maticas-org/maticas-data-logger/src/arduino/datalogger-esp32-dev-board/Event.cpp

#include "Event.h"

Event::Event() {
    type_ = UNKNOWN_EVENT; // Initialize with an unknown type
    statusCode_ = -1;
    timestamp_ = "";
    data_ = "{}";
}

Event::Event(int type,
             int statusCode,
             const String& timestamp,
             const String& data) {
    type_ = type;
    statusCode_ = statusCode;
    timestamp_ = timestamp;
    data_ = data;
}

Event::Event(String eventString){

    //parse the string to get the event attributes
    int typeIndex = eventString.indexOf("\"type\":") + 7;
    int statusCodeIndex = eventString.indexOf("\"statusCode\":") + 14;
    int timestampIndex = eventString.indexOf("\"datetime\":\"") + 12;
    int dataIndex = eventString.indexOf("\"data\":") + 7;

    type_ = eventString.substring(typeIndex, eventString.indexOf(",", typeIndex)).toInt();
    statusCode_ = eventString.substring(statusCodeIndex, eventString.indexOf(",", statusCodeIndex)).toInt();
    timestamp_ = eventString.substring(timestampIndex, eventString.indexOf("\",", timestampIndex));
    data_ = eventString.substring(dataIndex, eventString.indexOf("timesSent") - 2);
    timesSent = eventString.substring(eventString.indexOf("timesSent") + 11, eventString.indexOf("}", eventString.indexOf("timesSent"))).toInt();
}

int Event::getType() const {
    return type_;
}

int Event::getStatusCode() const {
    return statusCode_;
}

String Event::getTimestamp() const {
    return timestamp_;
}

String Event::getData() const {
    return data_;
}

void Event::setTimestamp(const String& timestamp) {
    timestamp_ = timestamp;
}


String Event::toString() const {

    //json like string representation
    String eventString = "{";
    eventString += "\"type\":";
    eventString += type_;
    eventString += ",\"statusCode\":";
    eventString += statusCode_;
    eventString += ",\"datetime\":\"";
    eventString += timestamp_;
    eventString += "\",\"data\":";
    
    //if data is empty write ""
    if (data_ == ""){
        eventString += "\"\"";
    }else{
        eventString += data_;
    }

    //add the timesSent attribute
    eventString += ",\"timesSent\":";
    eventString += timesSent;
    eventString += "}";
    eventString += "\n";

    return eventString;
}

bool Event::operator==(const Event& other) const {
    return (type_ == other.type_ && statusCode_ == other.statusCode_ && timestamp_ == other.timestamp_ && data_ == other.data_);
}

bool Event::operator!=(const Event& other) const {
    return !(*this == other);
}
